naman-tanwar/Solid-State-Tesla-Coil/Photos/Bare Hand Touching.jpg

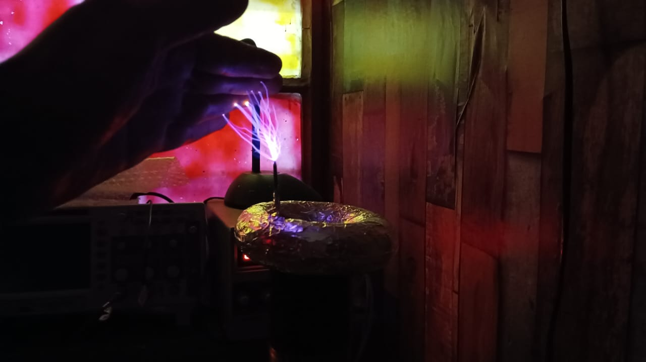
Photos/Bare Hand Touching.jpg
