naman-tanwar/Solid-State-Tesla-Coil/Photos/Renders/Coil Holder.png

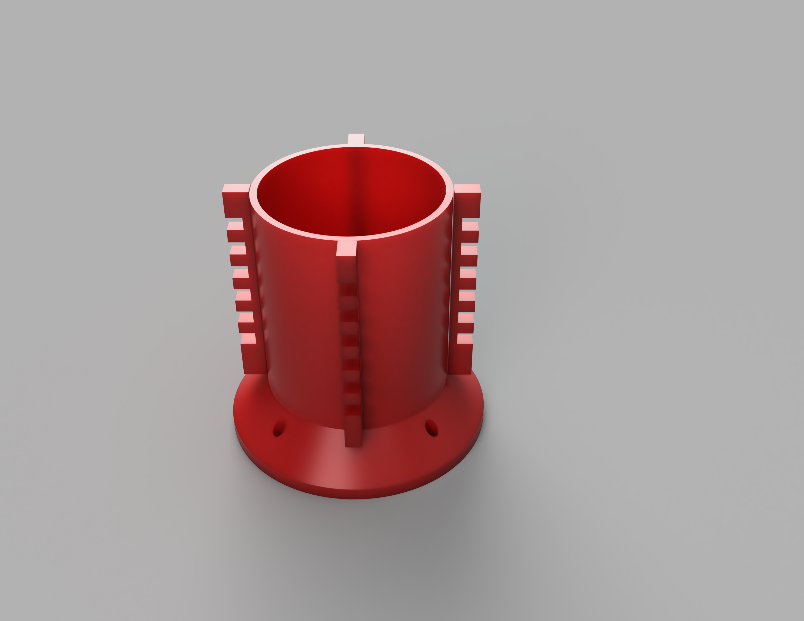
Photos/Renders/Coil Holder.png
