naman-tanwar/Solid-State-Tesla-Coil/Photos/Renders/Top-Load.png

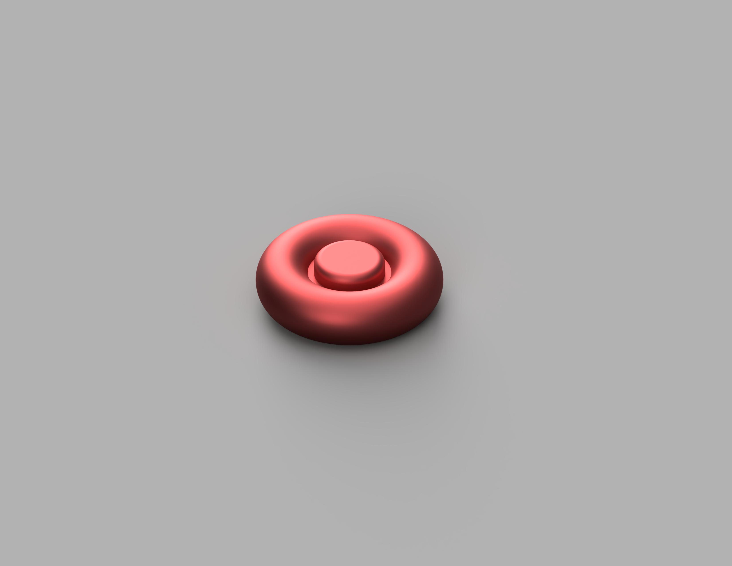
Photos/Renders/Top-Load.png
