naman-tanwar/Solid-State-Tesla-Coil/Photos/Scope Reading/Interrupted drive signal at 20%dc.bmp

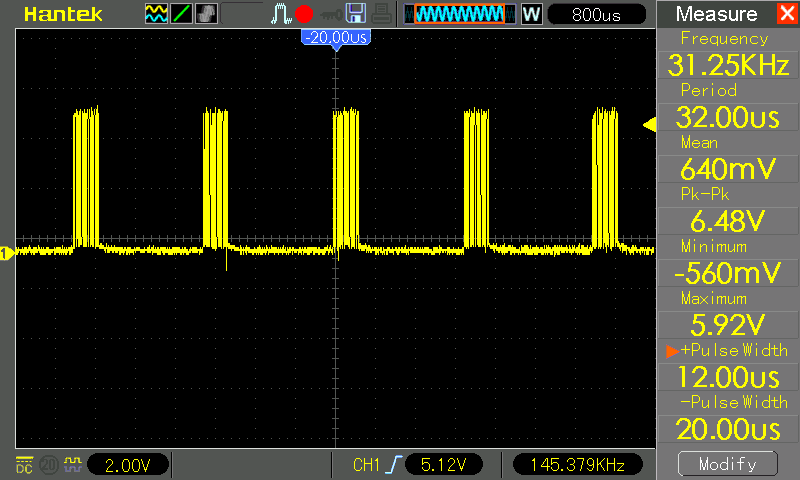
Photos/Scope Reading/Interrupted drive signal at 20%dc.bmp
