naman-tanwar/Solid-State-Tesla-Coil/Photos/Scope Reading/Interrupted drive signal at 50%dc.bmp.bmp

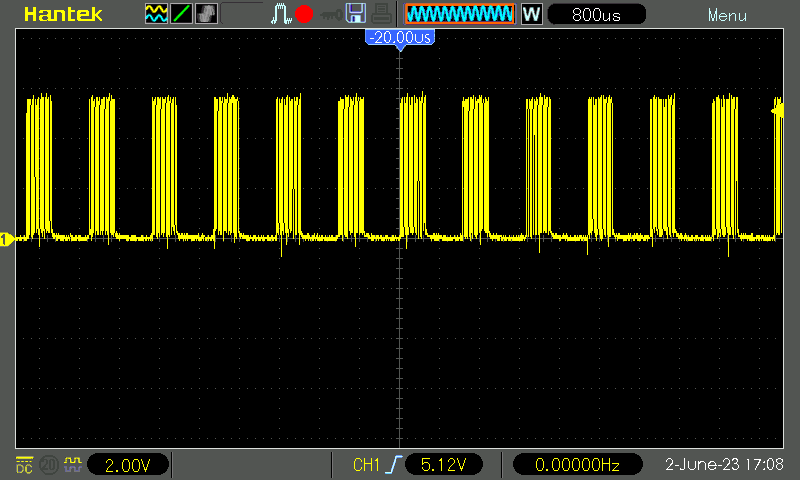
Photos/Scope Reading/Interrupted drive signal at 50%dc.bmp.bmp
