naman-tanwar/Solid-State-Tesla-Coil/Photos/Tesla Coil - 2.jpg

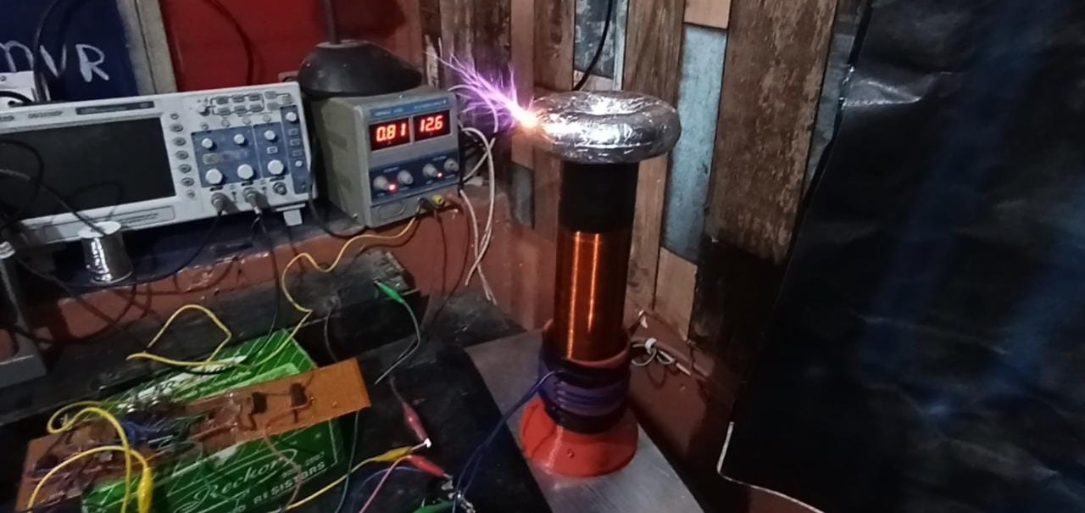
Photos/Tesla Coil - 2.jpg
