naman-tanwar/Solid-State-Tesla-Coil/Photos/Tesla Coil - 5.jpg

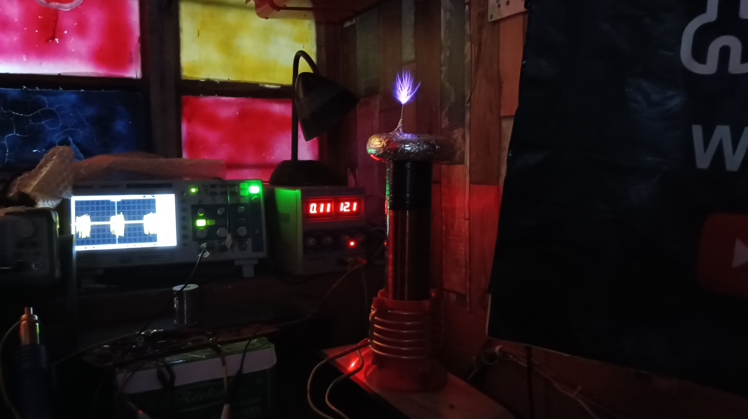
Photos/Tesla Coil - 5.jpg
