naman-tanwar/Solid-State-Tesla-Coil/Photos/Tesla Coil - 6.jpg

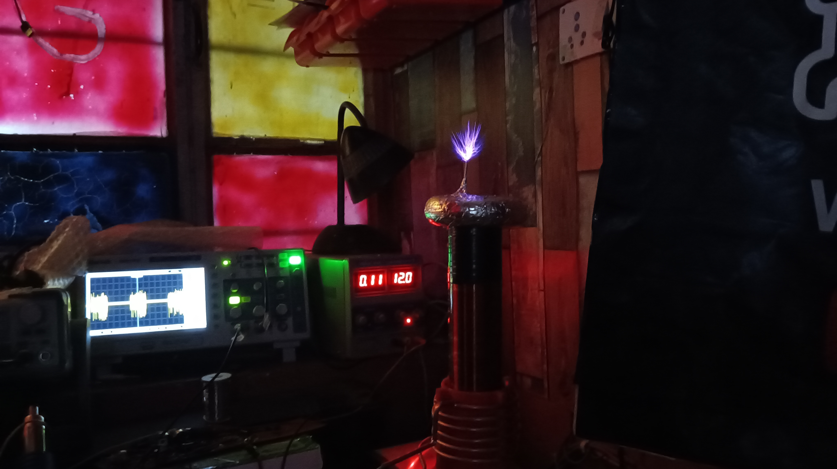
Photos/Tesla Coil - 6.jpg
