naman-tanwar/Solid-State-Tesla-Coil/Photos/Tesla Coil - 7.jpg

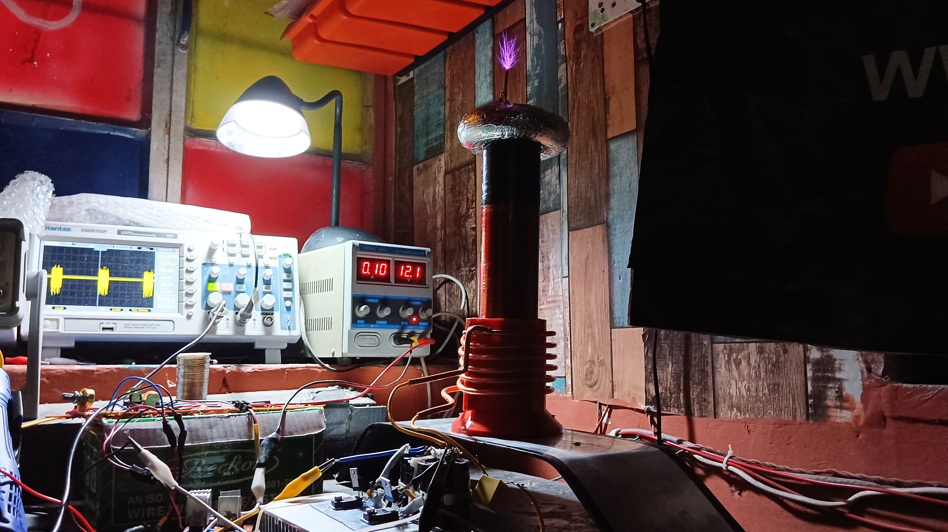
Photos/Tesla Coil - 7.jpg
