naman-tanwar/Solid-State-Tesla-Coil/Photos/Tesla Coil - 8.jpg

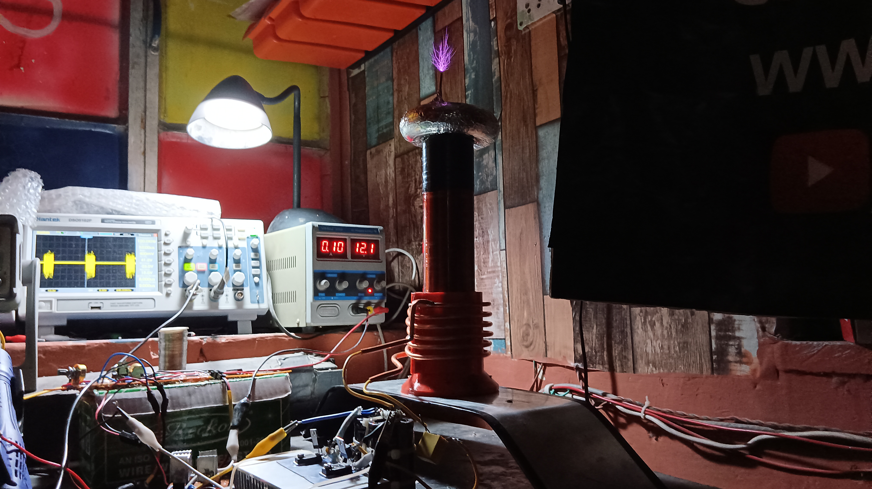
Photos/Tesla Coil - 8.jpg
