naman-tanwar/Solid-State-Tesla-Coil/Photos/Setup - Pic1.jpg

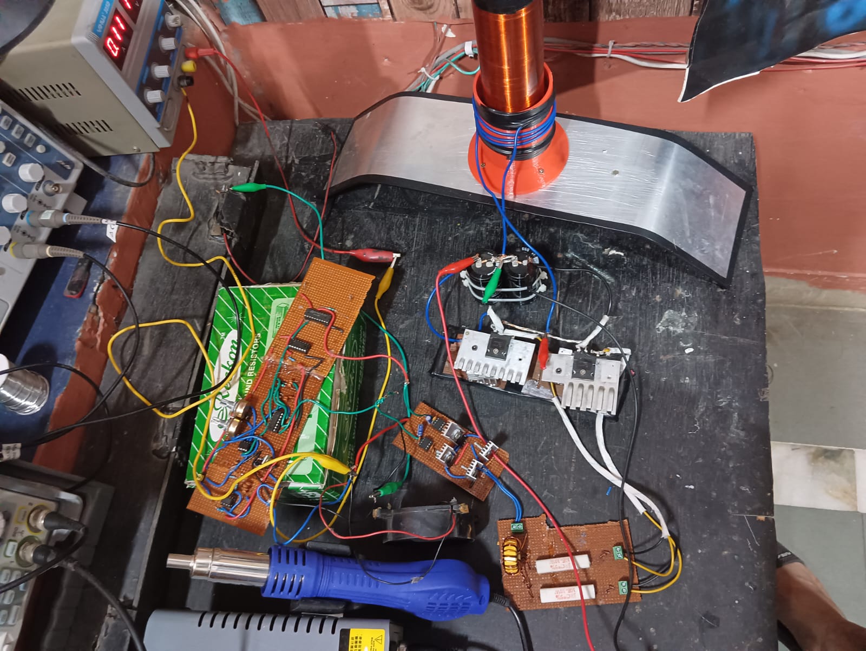
Photos/Setup - Pic1.jpg
