naman-tanwar/Solid-State-Tesla-Coil/Photos/Setup - Pic4.jpg

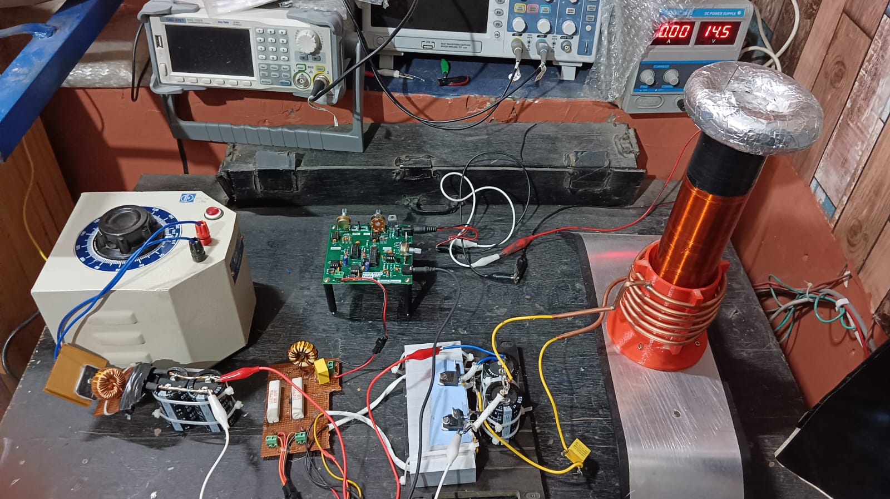
Photos/Setup - Pic4.jpg
