naman-tanwar/Solid-State-Tesla-Coil/Simulations/Gate Drive Signal Generation/Tesla_coil_Gate_Drive_Signal_Generation.asc

A1: schmtinv; Vhigh = 5V
A2: schmtinv; Vhigh = 5V
A3: schmtinv; Vhigh = 5V
A4: schmtinv; Vhigh = 5V
A5: schmtinv; Vhigh = 5V
A6: schmtinv; Vhigh = 5V
A8: buf1; Vhigh = 5V
A9: and; Vhigh = 5V
C1: cap; 0.01µ
C2: cap; 0.0002µ
C3: cap; 0.0003µ
C4: cap; 0.0003µ
C5: cap; 0.01µ
C6: cap; 0.3µ
D1: diode
D2: diode
D3: diode
D4: diode
R1: res; 3000
R2: res; 3000
R3: res; 1000
R4: res; 1000
R5: res; 1K
R6: res; 10K
R7: res; 1k
R8: res; 1k
U1: NE555
U2: NE555
V1: voltage; 5
Named nets: 0, VCC, Trig, out, OUT1, Drive1, Drive2
.tran 15m
Main Clock
Interrupter 1Khz
Drive Signals
Tesla Coil Drive Signal Generation
5K pot + 0.0002uF -->> 1.71Mhz to 520KHZ
Note:
-> Drive1 is complementary of Drive2 with a little "dead time".
-> R1, R2 are potentiometers to tune the frequency. 
-> R6 can be used to ajust the duty cycle of the interrupter
