naman-tanwar/Solid-State-Tesla-Coil/Simulations/LC Frequency Analysis/LC Frequency Analysis.asc

C1: cap; 30p
L1: ind; 1.792m
R: res; 30
V1: voltage; ""; AC 80
Named nets: 0, vin, vout
.ac lin 100000000000 600000 800000
;tran 1m
At730K 
C = 26.55pF
