naman-tanwar/Solid-State-Tesla-Coil/Simulations/Music Input/MusicSignaltoPWM.asc

C1: cap; 0.1µ
C2: cap; 0.1µ
C3: cap; 0.1µ
C4: cap; 0.1µ
R1: res; 100k
R2: res; 100k
R3: res; 100k
R5: res; 1k
R6: res; 100k
R7: res; 1000000
R8: res; 10K
R11: res; 220k
U1: OP777
U2: OP777
V1: voltage; 5
V2: voltage; SINE(0 0.8 100)
Named nets: 5V, 0, PWMOutput, AmplifierOutput, SignalInput
.tran 100m
POT
OPAMP based music signal to PWM signal (For Tesla Coil Interrupter)
Amplifier Stage
Comparator Stage
