naman-tanwar/Solid-State-Tesla-Coil/Simulations/Slayer Exciter/Slayer Exciter.asc

C1: cap; 1p
D1: diode
L1: ind2; 4.47µ
L2: ind2; 99.9m
Q1: npn; 2N3904
R2: res; 22k
V1: voltage; 10; Rser=1
Named nets: 0
.tran .1m startup
K L1 L2 1
TRADITIONAL SLAYER EXCITER
