naman-tanwar/Solid-State-Tesla-Coil/Simulations/Diode Voltage Limiting/Diode Voltage Limiting.asc

D1: diode; VS-E5TH0812
D2: diode; VS-E5TH0812
D3: diode; VS-E5TH0812
D4: diode; VS-E5TH0812
L1: ind; 1m
R1: res; 20
R2: res; 20
V1: voltage; PULSE(0 14 0 0 0 0.005m .01m)
V2: voltage; 10
V: voltage; PULSE(14 0 0 0 0 0.005m .01m)
Named nets: 0, 10V
.tran 1m
Voltage Limiting using Diodes Simulation
