naman-tanwar/Solid-State-Tesla-Coil/Simulations/Feedback tesla coil/Feedback tesla coil.asc

A1: schmtinv; Vhigh = 5V
A2: schmtinv; Vhigh = 5V
C1: cap; 1p
C2: cap; 5µ
D1: diode; 1N4148
D2: diode
D3: diode; 1N4148
D4: diode; 1N4148
D5: diode
L1: ind2; 4.47µ
L2: ind2; 99.9m
L3: ind2; 20µ
Q1: npn; 2N3904
Q2: npn; 2N3904
R1: res; 33K
R2: res; 100K
R3: res; 1K
R4: res; 10K
R5: res; 10K
V1: voltage; 10; Rser=1
V2: voltage; 5; Rser=1
V3: voltage; PULSE(5 0 0 10p 10p 0.32m 4m)
V4: voltage; 5
V5: voltage; 5
Named nets: 0, VCC, 5V, Mid, Out, Q2Base, Q1Base, Antenna, InterruptedFeedback
.tran 10m startup
K L1 L2 L3 1
Solid State Tesla Coil with Feedback
by NAMAN TANWAR
Note:
1. 2N3904 is used for simulation purpose only. 
    In reality, 60N100ND1 IGBT was used with gate drivers and gate transformer.
2. VCC will be much higher than 10v. About 60-240V.
3. V4 and V5 are shown to create "Mid" Voltage.
     In reality, capacitor banks of 660uF was used in the same fashion.
4. Antenna was shown as another transformer coil for simulation purposes.
